Manideep136/GPS-Tracker-using-STM32/STM32 GPS Tracker/doc/Layout1.1.png

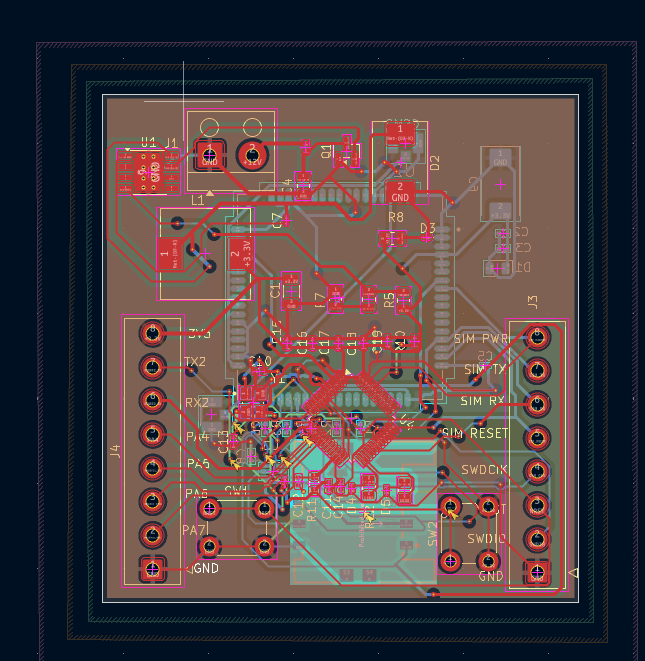
STM32 GPS Tracker/doc/Layout1.1.png
