Manideep136/GPS-Tracker-using-STM32/STM32 GPS Tracker/doc/Top.png

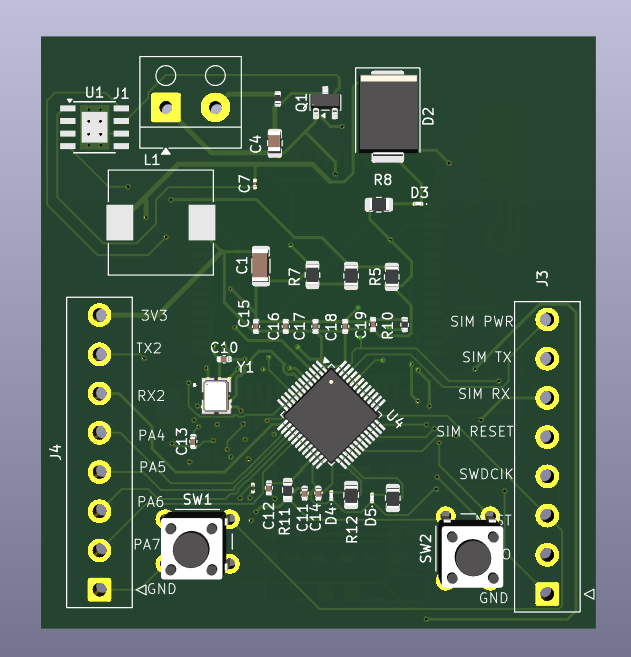
STM32 GPS Tracker/doc/Top.png
